pricna/Software-Defined-Radio-Receiver/Images/PCB_v1.1_Back.png

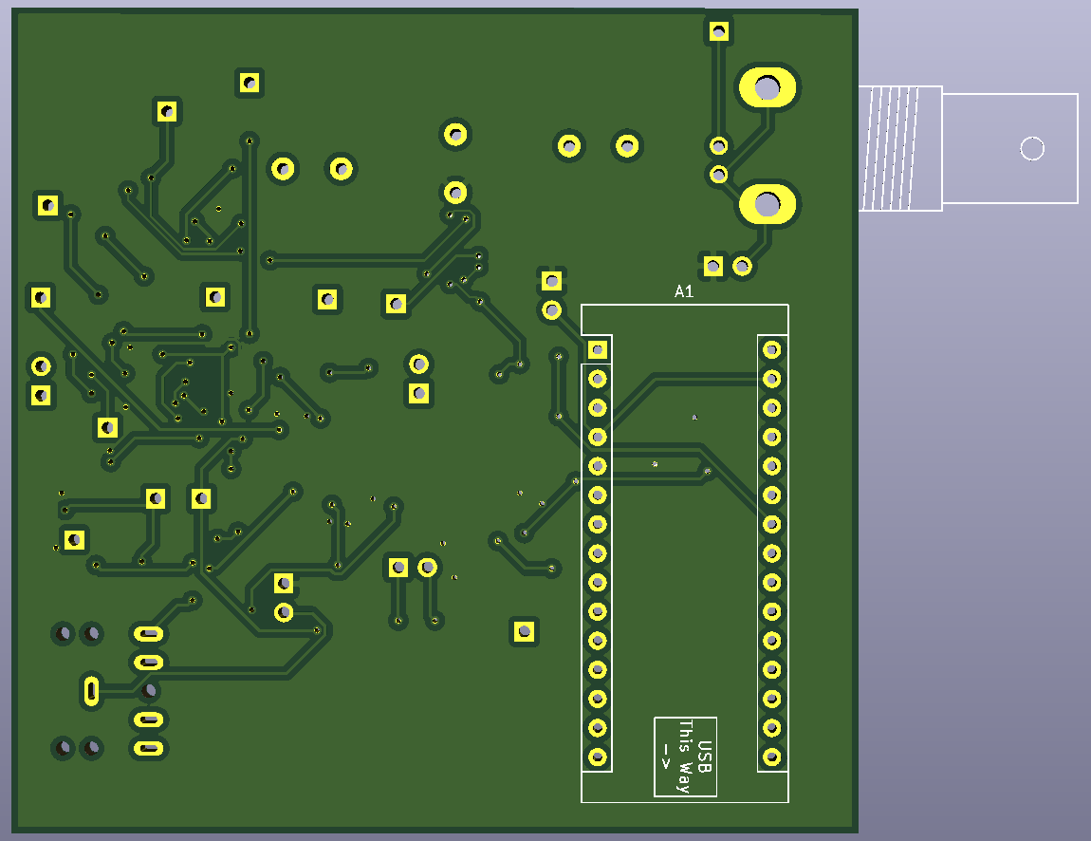
Images/PCB_v1.1_Back.png
