pricna/Software-Defined-Radio-Receiver/Project Files/v1.1/SDR_3D_1.png

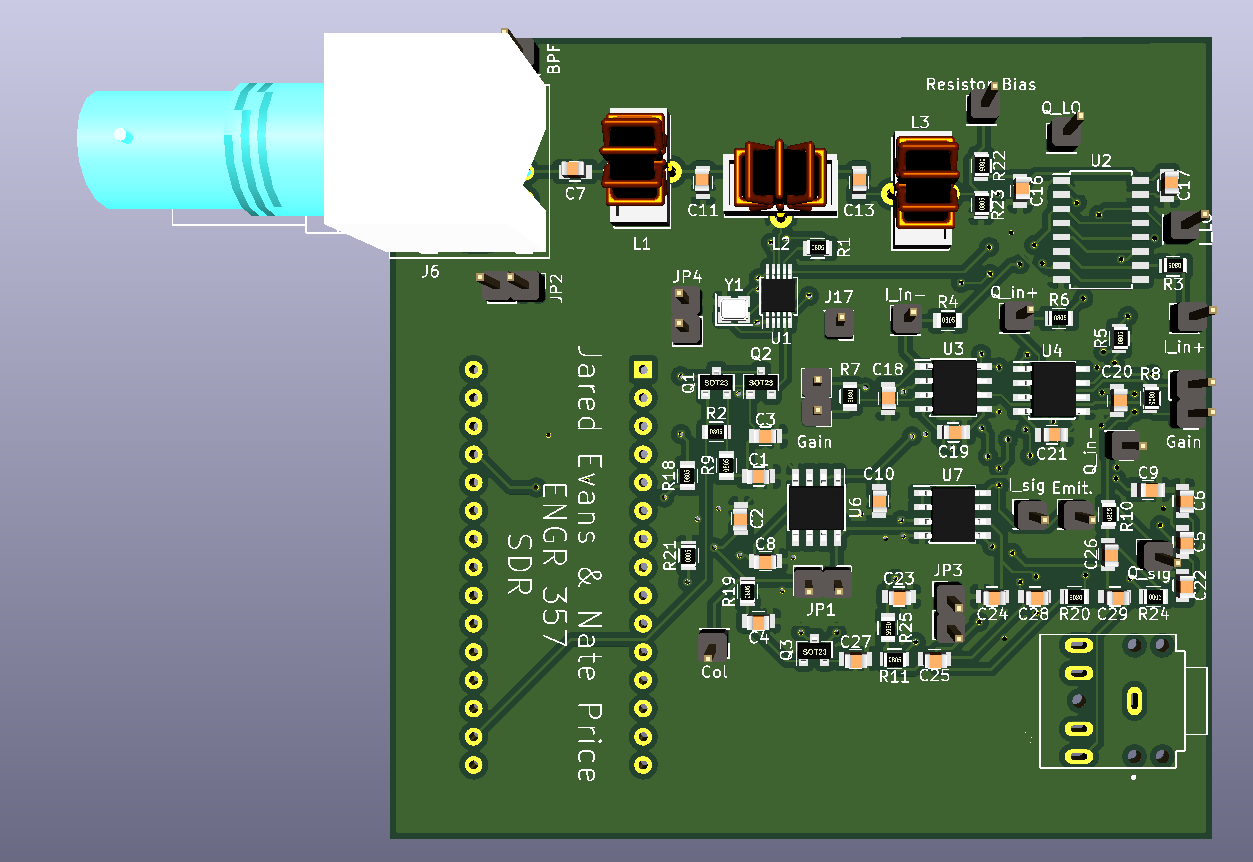
Project Files/v1.1/SDR_3D_1.png
