pricna/Software-Defined-Radio-Receiver/Project Files/v1.1/SDR_3D_2.png

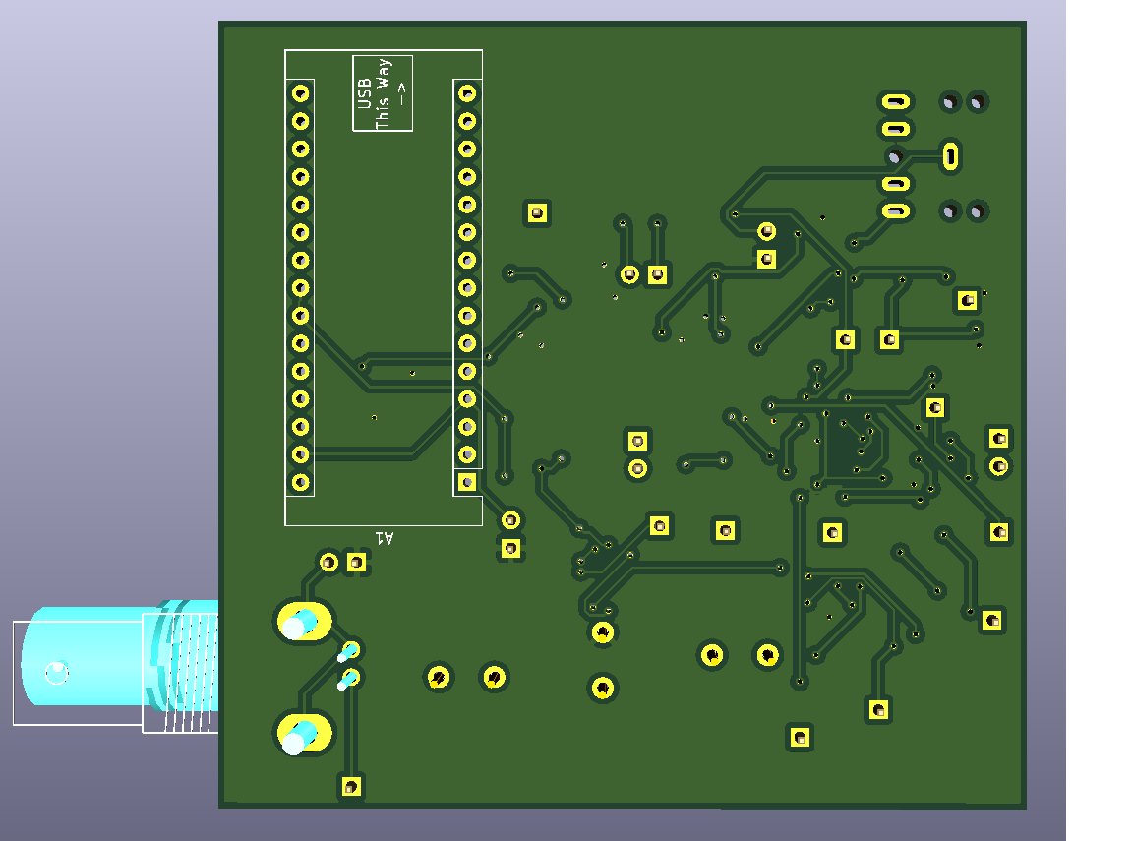
Project Files/v1.1/SDR_3D_2.png
