pricna/Software-Defined-Radio-Receiver/LTspice Simulation Files/MainCircuitSimulation.asc

C1: cap; 10µ
C2: cap; 120p
C3: cap; 1.1n
C4: cap; 120p
C5: cap; 100p
C6: cap; 100p
C7: cap; 100p
C8: cap; 100p
C9: cap; 10µF
C10: cap; 100p
C11: cap; 100p
C12: cap; 100p
C13: cap; .1µ
C14: cap; 100p
C15: cap; 10µ
C16: cap; .1µ
L1: ind; 1.3µ
L2: ind; 150n
L3: ind; 1.3µ
R1: res; 50
R2: res; 50
R3: res; 10k
R4: res; 10k
R5: res; 50
R6: res; 50
R7: res; 50
R8: res; 50
R9: res; 50
R10: res; 50
R11: res; 16k
R12: res; 16k
R13: res; 55k
R14: res; 55k
R15: res; 16k
R16: res; 100
R17: res; 16k
R18: res; 100
U1: LT1167
U2: LT1167
U3: LT6231
U6: LT6231
V1: voltage; SINE(0 5u 10meg)
V2: voltage; SINE(0 5u 10meg)
V3: voltage; 5V
V4: voltage; 5V
V5: voltage; SINE(0 5m 10meg); Rser=50
Named nets: 0, 5V, -5V, V_messy, V_ideal, V_unfiltered, AGND, V_filtered, 01, 10, I_output, Q_output
;noise V(I_output) V5 dec 100 10 100meg
Added Lowpass filter
.inc LM4562Fixed.LIB
.tran 0 1m 0m 0.5u
