pricna/Software-Defined-Radio-Receiver/LTspice Simulation Files/CorrectedBandPassSimulation.asc

C1: cap; 354p
C2: cap; 515p
C3: cap; 54.2p
L1: ind; 448n
L2: ind; 308n
L3: ind; 2.92µ
R1: res; 50
R2: res; 50
V1: voltage; 5V; AC 2
Named nets: 0, Corrected_FIlter
.ac dec 100 5meg 30meg
Corrected Bandpass Filter Simulation
