pricna/Software-Defined-Radio-Receiver/LTspice Simulation Files/LowPassFilterSimulation_1.asc

C1: cap; 0.1µ
C2: cap; 1n
C3: cap; 22.6n
R1: res; 866
R2: res; 1.1k
R3: res; 8.66k
R4: res; 50
U1: OP213
V1: voltage; 4.3
V2: voltage; ""; AC 1
Named nets: 0, Vo
.ac dec 1000 100 100meg
Preliminary Low-Pass Filter SImulation
