pricna/Software-Defined-Radio-Receiver/LTspice Simulation Files/BandpassSimulation_1.asc

C1: cap; 1n
C2: cap; 1n
C3: cap; 220p
C4: cap; 1n
C5: cap; 220p
C6: cap; 1.3µ
L1: ind; 1.3µ
L2: ind; 1.3µ
R1: res; 50
R2: res; 50
V1: voltage; 5V; AC 0.5
Named nets: 0
.ac dec 100 1k 100meg
Preliminary Bandpass Filter Simulation
