pricna/Software-Defined-Radio-Receiver/LTspice Simulation Files/Noise Simulations/NoiseSimulation.asc

C1: cap; 10µ
C2: cap; 354p
C3: cap; 515p
C4: cap; 54.2p
C5: cap; 100p
C6: cap; 100p
C7: cap; 100p
C8: cap; 100p
C9: cap; 0.1µ
C10: cap; 0.1µ
L1: ind; 448n
L2: ind; 308n
L3: ind; 2.92µ
R1: res; 50
R2: res; 50
R3: res; 10k
R4: res; 10k
R5: res; 50
R6: res; 50
R7: res; 50
R8: res; 50
R9: res; 50
R10: res; 50
R11: res; 100
R12: res; 100
R13: res; 55k
R14: res; 55k
U1: LT1167
U2: LT1167
V1: voltage; SINE(0 5u 10meg)
V2: voltage; SINE(0 5u 10meg)
V3: voltage; 5V
V4: voltage; 5V
V5: voltage; SINE(0 5m 10meg); Rser=50
Named nets: 0, 5V, -5V, V_messy, V_ideal, V_unfiltered, AGND, V_filtered, 01, 10, Vout
.noise V(Vout) V5 dec 100 10 100meg
Corrected Bandpass Filter
Instrumentation Amplifiers for the I and Q signals
LT1167 amplifiers are used for the simulation since the INAB21IDs couldn't be found.
10-16 MHz Passband
